nguyenhoainam2707/DHA-1v2/src/apps/atApp_AI.h

#ifndef _Application_atApp_AI_
#define _Application_atApp_AI_
/* _____PROJECT INCLUDES____________________________________________________ */
#include "App.h"
#include "../services/atService_ADS1115.h"
#include "../src/obj/atObj_Param.h"
#include "../src/obj/atObj_Data.h"
// #include "../src/apps/atApp_Database.h"
/* _____DEFINITIONS__________________________________________________________ */

/* _____GLOBAL VARIABLES_____________________________________________________ */
TaskHandle_t Task_atApp_AI;
void atApp_AI_Task_Func(void *parameter);
///////////////////////////////////////////////Testing part//
/* _____GLOBAL FUNCTION______________________________________________________ */

/* _____CLASS DEFINITION_____________________________________________________ */

/**
 * This Application class is the application to manage the
 */
class App_AI : public Application
{
public:
	App_AI();
	~App_AI();

	static bool ads1115InitOke; // this variable will be set to true when the ADS1115 is initialized successfully

protected:
private:
	static void App_AI_Pend();
	static void App_AI_Start();
	static void App_AI_Restart();
	static void App_AI_Execute();
	static void App_AI_Suspend();
	static void App_AI_Resume();
	static void App_AI_End();
} atApp_AI;

bool App_AI::ads1115InitOke = false; // Initialize the ADS1115 status to false
/**
 * This function will be automaticaly called when a object is created by this class
 */
App_AI::App_AI(/* args */)
{
	_Pend_User = *App_AI_Pend;
	_Start_User = *App_AI_Start;
	_Restart_User = *App_AI_Restart;
	_Execute_User = *App_AI_Execute;
	_Suspend_User = *App_AI_Suspend;
	_Resume_User = *App_AI_Resume;
	_End_User = *App_AI_End;

	// change the ID of application
	ID_Application = 1;
	// change the application name
	Name_Application = (char *)"AI Application	";
	// change the ID of SNM
}
/**
 * This function will be automaticaly called when the object of class is delete
 */
App_AI::~App_AI()
{
}
/**
 * Pend to start is the first task of this application it will do prerequisite condition. In the debit mode, task will send information of application to terminal to start the application.
 */
void App_AI::App_AI_Pend()
{
	// atService_ADS1115.Debug();
}
/**
 * This start function will init some critical function
 */
void App_AI::App_AI_Start()
{
	atService_ADS1115.Run_Service();
	if (atApp_AI.User_Mode == APP_USER_MODE_DEBUG)
	{
		atService_ADS1115.Debug();
	}

	/*
	|      Gain       |        Voltage Range       |        	  Data rate                 |
	|-----------------|----------------------------|----------------------------------------|
	| GAIN_TWOTHIRDS  | -6.144V to +6.144V         | RATE_ADS1115_8SPS   :  8 samples/sec   |
	| GAIN_ONE        | -4.096V to +4.096V         | RATE_ADS1115_16SPS  : 16 samples/sec   |
	| GAIN_TWO        | -2.048V to +2.048V         | RATE_ADS1115_32SPS  : 32 samples/sec   |
	| GAIN_FOUR       | -1.024V to +1.024V         | RATE_ADS1115_64SPS  : 64 samples/sec   |
	| GAIN_EIGHT      | -0.512V to +0.512V         | RATE_ADS1115_128SPS : 128 samples/sec  |
	| GAIN_SIXTEEN    | -0.256V to +0.256V         | RATE_ADS1115_250SPS : 250 samples/sec  |
	|                 |                            | RATE_ADS1115_475SPS : 475 samples/sec  |
	|                 |                            | RATE_ADS1115_860SPS : 860 samples/sec  |
	*/
	ads1115InitOke = Service_ADS1115::ADS1115_Init(GAIN_ONE, RATE_ADS1115_8SPS);
	if (ads1115InitOke)
	{
		if (atApp_AI.User_Mode == APP_USER_MODE_DEBUG)
		{
			Serial.println("ADS1115 init success!");
		}
	}
	else
	{
		if (atApp_AI.User_Mode == APP_USER_MODE_DEBUG)
		{
			Serial.println("ADS1115 init failed!");
		}
		for (int i = 0; i < 5; i++)
		{
			vTaskDelay(2000 / portTICK_PERIOD_MS); // Delay to allow the user to see the error message
			ads1115InitOke = Service_ADS1115::ADS1115_Init(GAIN_TWOTHIRDS, RATE_ADS1115_8SPS);
			if (atApp_AI.User_Mode == APP_USER_MODE_DEBUG)
			{
				Serial.println("Retry ADS1115 init...");
			}
			if (!ads1115InitOke)
			{
				Serial.println("ADS1115 init failed!");
			}
			else
			{
				if (atApp_AI.User_Mode == APP_USER_MODE_DEBUG)
				{
					Serial.println("ADS1115 reinitialize success!");
				}
				break; // Exit the retry loop if initialization is successful
			}
		}
		if (!ads1115InitOke)
		{
			if (atApp_AI.User_Mode == APP_USER_MODE_DEBUG)
			{
				Serial.println("Suspending AI task due to repeated initialization failure.");
			}
			vTaskSuspend(NULL); // Suspend the task if ADS1115 initialization fails again
		}
	}
}
/**
 * Restart function of SNM  app
 */
void App_AI::App_AI_Restart()
{
}
/**
 * Execute fuction of SNM app
 */
void App_AI::App_AI_Execute()
{
	for (uint8_t ai_index = 0; ai_index < MAX_AI_CHANNEL; ai_index++)
	{
		if (atObject_Param.ai_enable_list[ai_index])
		{
			atObject_Data.ai_raw[ai_index] = atService_ADS1115.ADS1115_readAI(ai_index);
			// from raw to voltage
			atObject_Data.ai_voltage[ai_index] = atService_ADS1115.computeVolts(atObject_Data.ai_raw[ai_index]); // assuming gain is GAIN_ONE
			// from voltage to current 4-20mA
			atObject_Data.ai_current[ai_index] = atService_ADS1115.computeCurrent(atObject_Data.ai_voltage[ai_index]);

			// atObject_Data.ai_current[ai_index] = atService_ADS1115.ADS1115_readAI_Current(ai_index);
			// atObject_Data.ai_voltage[ai_index] = atService_ADS1115.ADS1115_readAI_Voltage(ai_index);
		}
	}
	vTaskDelay(1000 * atObject_Param.ai_refresh_rate / portTICK_PERIOD_MS);

	if (atApp_AI.User_Mode == APP_USER_MODE_DEBUG)
	{
		// print all ar current values
		for (uint8_t ai_index = 0; ai_index < MAX_AI_CHANNEL; ai_index++)
		{
			if (atObject_Param.ai_enable_list[ai_index])
			{
				Serial.print("AI Channel ");
				Serial.print(ai_index);
				Serial.print(": ");
				Serial.print(atObject_Data.ai_current[ai_index]);
				Serial.println(" mA");
			}
		}
	}
}
void App_AI::App_AI_Suspend() {}
void App_AI::App_AI_Resume() {}
void App_AI::App_AI_End() {}
void atApp_AI_Task_Func(void *parameter)
{
	while (1)
	{
		atApp_AI.Run_Application(APP_RUN_MODE_AUTO);
		vTaskDelay(1000 / portTICK_PERIOD_MS);
	}
}
#endif
